deninur2427/ecu_pnm/docs/summaries/f103rb_nucleo/images/batt.jpg

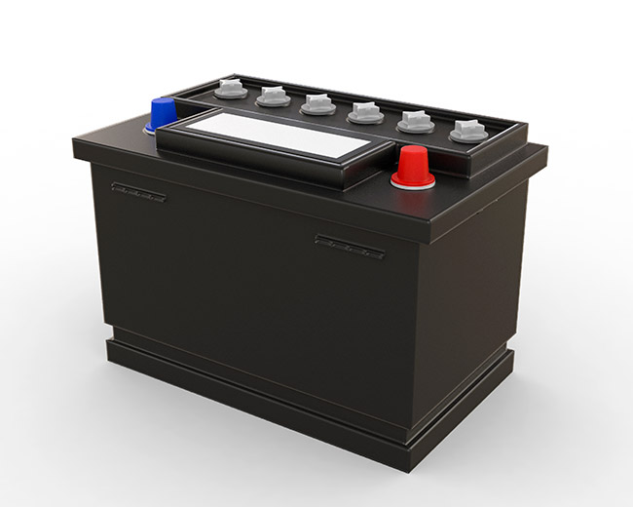
docs/summaries/f103rb_nucleo/images/batt.jpg
