deninur2427/ecu_pnm/docs/summaries/lqfp64/images/ecupnm.png

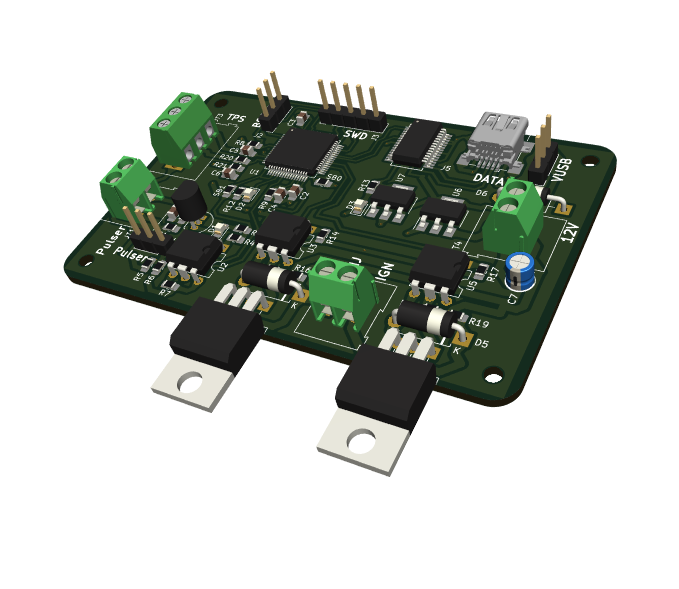
docs/summaries/lqfp64/images/ecupnm.png
