deninur2427/ecu_pnm/docs/summaries/lqfp64/images/unit_flat.png

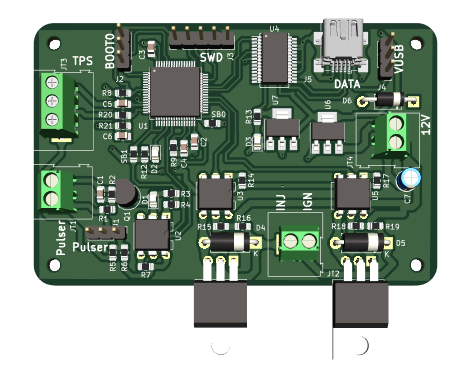
docs/summaries/lqfp64/images/unit_flat.png
