deninur2427/ecu_pnm/firmware/ecu/ecu_engine.h

/**
 * @file ecu_engine.h
 * @brief Engine Routine header
 *
 * @addtogroup ENGINE
 * @{
 */

#ifndef _ECU_ENGINE_H_
#define _ECU_ENGINE_H_

/**
 * @brief Whether Engine Data from Memory
 */
#define ENGINE_DATA_MEMORY          TRUE

// Engine Tooth Numbering
#define ENGINE_TOOTH_TOP            23
#define ENGINE_TOOTH_BOTTOM         9
#define ENGINE_TOOTH_INTAKE_OPEN    11
#define ENGINE_TOOTH_INTAKE_CLOSE   2
#define ENGINE_TOOTH_COIL_ON        19
#define ENGINE_TOOTH_COIL_OFF       20 // coil must be charged only in one tooth duration
#define ENGINE_TOOTH_EXHAUST_OPEN   18
#define ENGINE_TOOTH_EXHAUST_CLOSE  6

#define ENGINE_INJ_USETIMER         FALSE
#define ENGINE_IGN_USETIMER         FALSE

/**
 * @brief Amount of all Tooth
 * @details Tooth is 24 with 1 missing
 */
#define ENGINE_ALL_TOOTH    23

/**
 * @brief Degree of each engine tooth
 * @details Simetrically 360/24= 15
 */
#define ENGINE_DEGREE_TOOTH 15

/**
 * @brief Engine Data Matrix size in memory
 */
#define ENGINE_CDATA        12

/**
 * @brief Engine Crankshaft Tooth Calculation
 */
void ecu_ENG_ToothCalc(void);

/**
 * @brief Engine Injection and Ignition Calculation
 */
void ecu_ENG_InjIgnCalc(void);

/**
 * @brief Engine Injection and Ignition Control
 */
void ecu_ENG_InjIgnControl(void);

/**
 * @brief Engine Overflow status function
 */
void ecu_ENG_Overflow(void);

/**
 * @brief Send Engine Data through Serial Interface
 */
void ecu_ENG_DataSend(void);

#endif

/**  @} */
