deninur2427/ecu_pnm/firmware/ecu/ecu_shell.c

/**
 * @file ecu_shell.c
 * @brief Shell Interface code
 *
 * @addtogroup INTERFACE
 * @{
 */

#include "ecu_includes.h"

extern adcsample_t adc_tps_val;
extern icucnt_t rpm;
extern uint8_t toothcount;

thread_t *shelltp = NULL;

static void cmd_test(BaseSequentialStream *chp, int argc, char *argv[]){
    (void) argv;

    if(argc==0) chprintf(chp, "Serial Interface Working\r\n");
    return;
}

static void cmd_basic(BaseSequentialStream *chp, int argc, char *argv[]){
    (void) argv;

    // testing purpose
    //rpm = adc_tps_val / 100;

    if(argc==0) chprintf(chp,"%i,%i,%i\n",adc_tps_val,rpm,toothcount);
    return;
}

static const ShellCommand commands[] = {
    {"test",cmd_test},
    {"basic",cmd_basic},
    {NULL,NULL}
};

static const ShellConfig shell_cfg = {
    (BaseSequentialStream *)&SD1,
    commands
};

void ecu_SHELL_Init(void){
#ifdef F103RBNUCLEO
    palSetPadMode(GPIOA, 9, PAL_MODE_STM32_ALTERNATE_PUSHPULL);
    palSetPadMode(GPIOA, 10, PAL_MODE_INPUT);
#endif

#ifdef F051R8NUCLEO
    palSetPadMode(GPIOA, 9, PAL_MODE_ALTERNATE(1));
    palSetPadMode(GPIOA, 10, PAL_MODE_ALTERNATE(1));
#endif

    sdStart(&SD1, NULL);
    shellInit();

    chprintf((BaseSequentialStream*)&SD1,"Serial Shell Running\r\n");
}

void ecu_SHELL_Loop(void){
    if(!shelltp){
        shelltp = shellCreate(&shell_cfg, SHELL_WA_SIZE, NORMALPRIO);
    }
    else if(chThdTerminatedX(shelltp)){
        chThdRelease(shelltp);
        shelltp = NULL;
    }
}

/**  @} */
