deninur2427/ecu_pnm/firmware/ecu/ecu_gpt.h

/**
 * @file ecu_gpt.h
 * @brief General Purpose Timer header
 *
 * @addtogroup TIMER
 * @{
 */

#ifndef _ECU_GPT_H_
#define _ECU_GPT_H_

#define F_GPT 100000

/**
 * @brief General Purpose Timer Initialization
 */
void ecu_GPT_Init(void);

#endif // ECU_GPT_H

/**  @} */
